tguyenn/Digital-Synthesizer/firmware/firmware_v1/Launchpad/Lab7_slidepot.png

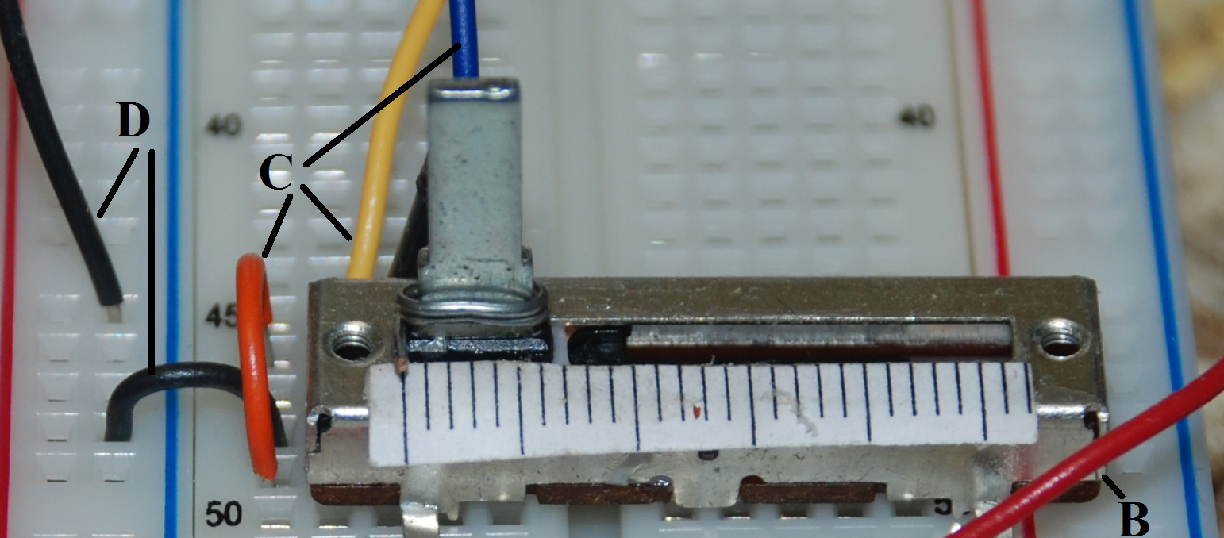
firmware/firmware_v1/Launchpad/Lab7_slidepot.png
