tguyenn/Digital-Synthesizer/firmware/inc/Motor.h

/*!
 * @defgroup RSLK
 * @brief RSLK motor interface
 <table>
<caption id="RSLKmotor pins">RSLK motor pins</caption>
<tr><th> TM4C <th> MSPM0  <th> Description
<tr><td> PF2  <td> PB4  <td> Motor_PWML, ML+, IN3, PB.4/TIMA1_C0;
<tr><td> PF3  <td> PB1  <td> Motor_PWMR, MR+, IN1, PB.1/TIMA1_C1;
<tr><td> PA3  <td> PB0  <td> Motor_DIR_L,ML-, IN4, 1 means forward, 0 means backward
<tr><td> PA2  <td> PB16 <td> Motor_DIR_R,MR-, IN2
</table>
 * @{*/
/**
 * @file      Motor.h
 * @brief     RSLK dual H-bridge driver
 * @details   RSLK motor interface<br>

 * @version   RSLK v2.02
 * @author    Daniel Valvano and Jonathan Valvano
 * @copyright Copyright 2024 by Jonathan W. Valvano, valvano@mail.utexas.edu,
 * @warning   AS-IS
 * @note      For more information see  http://users.ece.utexas.edu/~valvano/
 * @date      July 1, 2024
 <table>
<caption id="RSLKmotor2">RSLK motor pins</caption>
<tr><th> TM4C <th> MSPM0  <th> Description
<tr><td> PF2  <td> PB4  <td> Motor_PWML, ML+, IN3, PWM M1PWM6
<tr><td> PF3  <td> PB1  <td> Motor_PWMR, MR+, IN1, PWM M1PWM7
<tr><td> PA3  <td> PB0  <td> Motor_DIR_L,ML-, IN4, GPIO, 0 means forward, 1 means backward
<tr><td> PA2  <td> PB16 <td> Motor_DIR_R,MR-, IN2, GPIO, 0 means forward, 1 means backward
</table>
  ******************************************************************************/


#ifndef __MOTOR_H__
#define __MOTOR_H__
#include <stdint.h>
#define MOTOR_PERIOD 40000 // 12.5*4=50ns, 2ms
#define MOTORMIN 2
#define MOTORMAX (MOTOR_PERIOD-2)
/**
 * Initialize RSLK motors
 * PWM clock set to 50ns (divide by 4)
 * @param none
 * @return none
 * @brief  Initialize motors
 * @note period is 2000 us
 */
void Motor_Init(void);

/**
 * Set RSLK motor power forward<br>
 * @param dutyLeft MOTORMIN to MOTORMAX
 * @param dutyRight MOTORMIN to MOTORMAX
 * @return none
 * @note period is 10000 us
 * @brief  Go forward
 */
void Motor_Forward(uint32_t dutyLeft, uint32_t dutyRight);

/**
 * Set RSLK motor power backward<br>
 * @param dutyLeft MOTORMIN to MOTORMAX
 * @param dutyRight MOTORMIN to MOTORMAX
 * @return none
 * @note period is 2000 us
 * @brief  Go backward
 */
void Motor_Backward(uint32_t dutyLeft, uint32_t dutyRight);

/**
 * Set RSLK motor power right turn<br>
 * @param dutyLeft MOTORMIN to MOTORMAX
 * @param dutyRight MOTORMIN to MOTORMAX
 * @return none
 * @note period is 2000 us
 * @brief  Turn right
 */
void Motor_Right(uint32_t dutyLeft, uint32_t dutyRight);

/**
 * Set RSLK motor power left turn<br>
 * @param dutyLeft MOTORMIN to MOTORMAX
 * @param dutyRight MOTORMIN to MOTORMAX
 * @return none
 * @note period is 2000 us
 * @brief Turn left
 */
void Motor_Left(uint32_t dutyLeft, uint32_t dutyRight);

#endif
