tguyenn/Digital-Synthesizer/firmware/firmware_v1/inc/led_timer_regs.h

/*****************************************************************************

  Copyright (C) 2024 Texas Instruments Incorporated - http://www.ti.com/ 

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
   Neither the name of Texas Instruments Incorporated nor the names of
   its contributors may be used to endorse or promote products derived
   from this software without specific prior written permission.

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
*****************************************************************************/

#ifndef ti_devices_msp_peripherals_hw_gptimer__include
#define ti_devices_msp_peripherals_hw_gptimer__include

/* Filename: hw_gptimer.h */
/* Revised: 2024-06-04 10:48:04 */
/* Revision: a6be75578aae0bf7330b042a9fb5c36fc4988a43 */

#ifndef __CORTEX_M
  #ifdef __cplusplus
    #define __I  volatile        /*!< Defines 'read only' permissions */
  #else
    #define __I  volatile const  /*!< Defines 'read only' permissions */
  #endif
  #define __O  volatile          /*!< Defines 'write only' permissions */
  #define __IO  volatile         /*!< Defines 'read / write' permissions */

  /* following defines should be used for structure members */
  #define __IM  volatile const   /*! Defines 'read only' structure member permissions */
  #define __OM  volatile         /*! Defines 'write only' structure member permissions */
  #define __IOM  volatile        /*! Defines 'read / write' structure member permissions */
#endif

/* Use standard integer types with explicit width */
#include <stdint.h>

#ifdef __cplusplus
 extern "C" {
#endif

#if defined ( __CC_ARM )
#pragma anon_unions
#endif

/******************************************************************************
* GPTIMER Registers
******************************************************************************/
#define GPTIMER_COUNTERREGS_OFS                  ((uint32_t)0x00001800U)
#define GPTIMER_COMMONREGS_OFS                   ((uint32_t)0x00001100U)
#define GPTIMER_GEN_EVENT1_OFS                   ((uint32_t)0x00001080U)
#define GPTIMER_GEN_EVENT0_OFS                   ((uint32_t)0x00001050U)
#define GPTIMER_CPU_INT_OFS                      ((uint32_t)0x00001020U)
#define GPTIMER_GPRCM_OFS                        ((uint32_t)0x00000800U)


/** @addtogroup GPTIMER_COUNTERREGS
  @{
*/

typedef struct {
  __IO uint32_t CTR;                               /* !< (@ 0x00001800) Counter Register */
  __IO uint32_t CTRCTL;                            /* !< (@ 0x00001804) Counter Control Register */
  __IO uint32_t LOAD;                              /* !< (@ 0x00001808) Load Register */
       uint32_t RESERVED0;
  __IO uint32_t CC_01[2];                          /* !< (@ 0x00001810) Capture or Compare Register 0/1 */
  __IO uint32_t CC_23[2];                          /* !< (@ 0x00001818) Capture or Compare Register 2/3 */
  __IO uint32_t CC_45[2];                          /* !< (@ 0x00001820) The CC_45 register are a registers which can be
                                                      used as compare to the current CTR to create an events CC4U, CC4D,
                                                      CC5U and CC5D. */
       uint32_t RESERVED1[2];
  __IO uint32_t CCCTL_01[2];                       /* !< (@ 0x00001830) Capture or Compare Control Registers 0/1 */
  __IO uint32_t CCCTL_23[2];                       /* !< (@ 0x00001838) Capture or Compare Control Registers 2/3 */
  __IO uint32_t CCCTL_45[2];                       /* !< (@ 0x00001840) Capture or Compare Control Registers 4/5 */
       uint32_t RESERVED2[2];
  __IO uint32_t OCTL_01[2];                        /* !< (@ 0x00001850) CCP Output Control Registers 0/1 */
  __IO uint32_t OCTL_23[2];                        /* !< (@ 0x00001858) CCP Output Control Registers 2/3 */
       uint32_t RESERVED3[4];
  __IO uint32_t CCACT_01[2];                       /* !< (@ 0x00001870) Capture or Compare Action Registers 0/1 */
  __IO uint32_t CCACT_23[2];                       /* !< (@ 0x00001878) Capture or Compare Action Registers 2/3 */
  __IO uint32_t IFCTL_01[2];                       /* !< (@ 0x00001880) Input Filter Control Register 0/1 */
  __IO uint32_t IFCTL_23[2];                       /* !< (@ 0x00001888) Input Filter Control Register 2/3 */
       uint32_t RESERVED4[4];
  __IO uint32_t PL;                                /* !< (@ 0x000018A0) Phase Load Register */
  __IO uint32_t DBCTL;                             /* !< (@ 0x000018A4) Dead Band insertion control register */
       uint32_t RESERVED5[2];
  __IO uint32_t TSEL;                              /* !< (@ 0x000018B0) Trigger Select Register */
  __I  uint32_t RC;                                /* !< (@ 0x000018B4) Repeat counter Register */
  __IO uint32_t RCLD;                              /* !< (@ 0x000018B8) Repeat counter load Register */
  __I  uint32_t QDIR;                              /* !< (@ 0x000018BC) QEI Count Direction Register */
       uint32_t RESERVED6[4];
  __IO uint32_t FCTL;                              /* !< (@ 0x000018D0) Fault Control Register */
  __IO uint32_t FIFCTL;                            /* !< (@ 0x000018D4) Fault input Filter control register */
} GPTIMER_COUNTERREGS_Regs;

/*@}*/ /* end of group GPTIMER_COUNTERREGS */

/** @addtogroup GPTIMER_COMMONREGS
  @{
*/

typedef struct {
  __IO uint32_t CCPD;                              /* !< (@ 0x00001100) CCP Direction */
  __IO uint32_t ODIS;                              /* !< (@ 0x00001104) Output Disable */
  __IO uint32_t CCLKCTL;                           /* !< (@ 0x00001108) Counter Clock Control Register */
  __IO uint32_t CPS;                               /* !< (@ 0x0000110C) Clock Prescale Register */
  __I  uint32_t CPSV;                              /* !< (@ 0x00001110) Clock prescale count status register */
  __IO uint32_t CTTRIGCTL;                         /* !< (@ 0x00001114) Timer Cross Trigger Control Register */
       uint32_t RESERVED0;
  __O  uint32_t CTTRIG;                            /* !< (@ 0x0000111C) Timer Cross Trigger Register */
  __IO uint32_t FSCTL;                             /* !< (@ 0x00001120) Fault Source Control */
  __IO uint32_t GCTL;                              /* !< (@ 0x00001124) Global control register */
} GPTIMER_COMMONREGS_Regs;

/*@}*/ /* end of group GPTIMER_COMMONREGS */

/** @addtogroup GPTIMER_GEN_EVENT1
  @{
*/

typedef struct {
  __I  uint32_t IIDX;                              /* !< (@ 0x00001080) Interrupt index */
       uint32_t RESERVED0;
  __IO uint32_t IMASK;                             /* !< (@ 0x00001088) Interrupt mask */
       uint32_t RESERVED1;
  __I  uint32_t RIS;                               /* !< (@ 0x00001090) Raw interrupt status */
       uint32_t RESERVED2;
  __I  uint32_t MIS;                               /* !< (@ 0x00001098) Masked interrupt status */
       uint32_t RESERVED3;
  __O  uint32_t ISET;                              /* !< (@ 0x000010A0) Interrupt set */
       uint32_t RESERVED4;
  __O  uint32_t ICLR;                              /* !< (@ 0x000010A8) Interrupt clear */
} GPTIMER_GEN_EVENT1_Regs;

/*@}*/ /* end of group GPTIMER_GEN_EVENT1 */

/** @addtogroup GPTIMER_GEN_EVENT0
  @{
*/

typedef struct {
  __I  uint32_t IIDX;                              /* !< (@ 0x00001050) Interrupt index */
       uint32_t RESERVED0;
  __IO uint32_t IMASK;                             /* !< (@ 0x00001058) Interrupt mask */
       uint32_t RESERVED1;
  __I  uint32_t RIS;                               /* !< (@ 0x00001060) Raw interrupt status */
       uint32_t RESERVED2;
  __I  uint32_t MIS;                               /* !< (@ 0x00001068) Masked interrupt status */
       uint32_t RESERVED3;
  __O  uint32_t ISET;                              /* !< (@ 0x00001070) Interrupt set */
       uint32_t RESERVED4;
  __O  uint32_t ICLR;                              /* !< (@ 0x00001078) Interrupt clear */
} GPTIMER_GEN_EVENT0_Regs;

/*@}*/ /* end of group GPTIMER_GEN_EVENT0 */

/** @addtogroup GPTIMER_CPU_INT
  @{
*/

typedef struct {
  __I  uint32_t IIDX;                              /* !< (@ 0x00001020) Interrupt index */
       uint32_t RESERVED0;
  __IO uint32_t IMASK;                             /* !< (@ 0x00001028) Interrupt mask */
       uint32_t RESERVED1;
  __I  uint32_t RIS;                               /* !< (@ 0x00001030) Raw interrupt status */
       uint32_t RESERVED2;
  __I  uint32_t MIS;                               /* !< (@ 0x00001038) Masked interrupt status */
       uint32_t RESERVED3;
  __O  uint32_t ISET;                              /* !< (@ 0x00001040) Interrupt set */
       uint32_t RESERVED4;
  __O  uint32_t ICLR;                              /* !< (@ 0x00001048) Interrupt clear */
} GPTIMER_CPU_INT_Regs;

/*@}*/ /* end of group GPTIMER_CPU_INT */

/** @addtogroup GPTIMER_GPRCM
  @{
*/

typedef struct {
  __IO uint32_t PWREN;                             /* !< (@ 0x00000800) Power enable */
  __O  uint32_t RSTCTL;                            /* !< (@ 0x00000804) Reset Control */
       uint32_t RESERVED0[3];
  __I  uint32_t STAT;                              /* !< (@ 0x00000814) Status Register */
} GPTIMER_GPRCM_Regs;

/*@}*/ /* end of group GPTIMER_GPRCM */

/** @addtogroup GPTIMER
  @{
*/

typedef struct {
       uint32_t RESERVED0[256];
  __IO uint32_t FSUB_0;                            /* !< (@ 0x00000400) Subsciber Port 0 */
  __IO uint32_t FSUB_1;                            /* !< (@ 0x00000404) Subscriber Port 1 */
       uint32_t RESERVED1[15];
  __IO uint32_t FPUB_0;                            /* !< (@ 0x00000444) Publisher Port 0 */
  __IO uint32_t FPUB_1;                            /* !< (@ 0x00000448) Publisher Port 1 */
       uint32_t RESERVED2[237];
  GPTIMER_GPRCM_Regs  GPRCM;                             /* !< (@ 0x00000800) */
       uint32_t RESERVED3[506];
  __IO uint32_t CLKDIV;                            /* !< (@ 0x00001000) Clock Divider */
       uint32_t RESERVED4;
  __IO uint32_t CLKSEL;                            /* !< (@ 0x00001008) Clock Select for Ultra Low Power peripherals */
       uint32_t RESERVED5[3];
  __IO uint32_t PDBGCTL;                           /* !< (@ 0x00001018) Peripheral Debug Control */
       uint32_t RESERVED6;
  GPTIMER_CPU_INT_Regs  CPU_INT;                           /* !< (@ 0x00001020) */
       uint32_t RESERVED7;
  GPTIMER_GEN_EVENT0_Regs  GEN_EVENT0;                        /* !< (@ 0x00001050) */
       uint32_t RESERVED8;
  GPTIMER_GEN_EVENT1_Regs  GEN_EVENT1;                        /* !< (@ 0x00001080) */
       uint32_t RESERVED9[13];
  __IO uint32_t EVT_MODE;                          /* !< (@ 0x000010E0) Event Mode */
       uint32_t RESERVED10[6];
  __I  uint32_t DESC;                              /* !< (@ 0x000010FC) Module Description */
  GPTIMER_COMMONREGS_Regs  COMMONREGS;                        /* !< (@ 0x00001100) */
       uint32_t RESERVED11[438];
  GPTIMER_COUNTERREGS_Regs  COUNTERREGS;                       /* !< (@ 0x00001800) */
} GPTIMER_Regs;

/*@}*/ /* end of group GPTIMER */



#if defined ( __CC_ARM )
#pragma no_anon_unions
#endif

/******************************************************************************
* GPTIMER Register Control Bits
******************************************************************************/

/* GPTIMER_CTR Bits */
/* GPTIMER_CTR[CCTR] Bits */
#define GPTIMER_CTR_CCTR_OFS                     (0)                             /* !< CCTR Offset */
#define GPTIMER_CTR_CCTR_MASK                    ((uint32_t)0xFFFFFFFFU)         /* !< Current Counter value */
#define GPTIMER_CTR_CCTR_MINIMUM                 ((uint32_t)0x00000000U)         /* !< Minimum value */
#define GPTIMER_CTR_CCTR_MAXIMUM                 ((uint32_t)0xFFFFFFFFU)         /* !< Maximum Value */

/* GPTIMER_CTRCTL Bits */
/* GPTIMER_CTRCTL[EN] Bits */
#define GPTIMER_CTRCTL_EN_OFS                    (0)                             /* !< EN Offset */
#define GPTIMER_CTRCTL_EN_MASK                   ((uint32_t)0x00000001U)         /* !< Counter Enable.  This bit allows
                                                                                    the timer to advance  This bit is
                                                                                    automatically cleared if REPEAT=0 (do
                                                                                    not automatically reload) and the
                                                                                    counter value equals zero.  CPU
                                                                                    Write: A register write that sets the
                                                                                    EN bit, the counter value is set per
                                                                                    the CVAE value. Hardware: This bit
                                                                                    may also be set as the result of an
                                                                                    LCOND or ZCOND condition being met
                                                                                    and the counter value changed to the
                                                                                    load value or zero value,
                                                                                    respectively. */
#define GPTIMER_CTRCTL_EN_DISABLED               ((uint32_t)0x00000000U)         /* !< Disabled */
#define GPTIMER_CTRCTL_EN_ENABLED                ((uint32_t)0x00000001U)         /* !< Enabled */
/* GPTIMER_CTRCTL[REPEAT] Bits */
#define GPTIMER_CTRCTL_REPEAT_OFS                (1)                             /* !< REPEAT Offset */
#define GPTIMER_CTRCTL_REPEAT_MASK               ((uint32_t)0x0000000EU)         /* !< Repeat.  The repeat bit controls
                                                                                    whether the counter continues to
                                                                                    advance following a zero event, or
                                                                                    the exiting of a debug or fault
                                                                                    condition.  If counting down, a zero
                                                                                    event is followed by a load at the
                                                                                    next advance condition. If counting
                                                                                    up-down, a zero event is followed by
                                                                                    an advance event (+1). The intent of
                                                                                    encoding 3 is that if the debug
                                                                                    condition is in effect, the
                                                                                    generation of the load pulse is
                                                                                    deferred until the debug condition is
                                                                                    over. This allows the counter to
                                                                                    reach zero before counting is
                                                                                    suspended. */
#define GPTIMER_CTRCTL_REPEAT_REPEAT_0           ((uint32_t)0x00000000U)         /* !< Does not automatically advance
                                                                                    following a zero event. */
#define GPTIMER_CTRCTL_REPEAT_REPEAT_1           ((uint32_t)0x00000002U)         /* !< Continues to advance following a
                                                                                    zero event. */
#define GPTIMER_CTRCTL_REPEAT_REPEAT_2           ((uint32_t)0x00000004U)         /* !< Reserved */
#define GPTIMER_CTRCTL_REPEAT_REPEAT_3           ((uint32_t)0x00000006U)         /* !< Continues to advance following a
                                                                                    zero event if the debug mode is not
                                                                                    in effect, or following the release
                                                                                    of the debug mode. */
#define GPTIMER_CTRCTL_REPEAT_REPEAT_4           ((uint32_t)0x00000008U)         /* !< Reserved */
/* GPTIMER_CTRCTL[CM] Bits */
#define GPTIMER_CTRCTL_CM_OFS                    (4)                             /* !< CM Offset */
#define GPTIMER_CTRCTL_CM_MASK                   ((uint32_t)0x00000030U)         /* !< Count Mode */
#define GPTIMER_CTRCTL_CM_DOWN                   ((uint32_t)0x00000000U)         /* !< Down */
#define GPTIMER_CTRCTL_CM_UP_DOWN                ((uint32_t)0x00000010U)         /* !< Up/Down */
#define GPTIMER_CTRCTL_CM_UP                     ((uint32_t)0x00000020U)         /* !< Counter counts up. */
/* GPTIMER_CTRCTL[CVAE] Bits */
#define GPTIMER_CTRCTL_CVAE_OFS                  (28)                            /* !< CVAE Offset */
#define GPTIMER_CTRCTL_CVAE_MASK                 ((uint32_t)0x30000000U)         /* !< Counter Value After Enable.  This
                                                                                    field specifies the initialization
                                                                                    condition of the counter when the EN
                                                                                    bit is changed from 0 to 1 by a write
                                                                                    to the CTRCTL register. Note that an
                                                                                    external event can also cause the EN
                                                                                    bit to go active. */
#define GPTIMER_CTRCTL_CVAE_LDVAL                ((uint32_t)0x00000000U)         /* !< The counter is set to the LOAD
                                                                                    register value */
#define GPTIMER_CTRCTL_CVAE_NOCHANGE             ((uint32_t)0x10000000U)         /* !< The counter value is unchanged from
                                                                                    its current value which could have
                                                                                    been initialized by software */
#define GPTIMER_CTRCTL_CVAE_ZEROVAL              ((uint32_t)0x20000000U)         /* !< The counter is set to zero */
/* GPTIMER_CTRCTL[DRB] Bits */
#define GPTIMER_CTRCTL_DRB_OFS                   (17)                            /* !< DRB Offset */
#define GPTIMER_CTRCTL_DRB_MASK                  ((uint32_t)0x00020000U)         /* !< Debug Resume Behavior This bit
                                                                                    specifies what the device does
                                                                                    following the release/exit of debug
                                                                                    mode. */
#define GPTIMER_CTRCTL_DRB_RESUME                ((uint32_t)0x00000000U)         /* !< Resume counting */
#define GPTIMER_CTRCTL_DRB_CVAE_ACTION           ((uint32_t)0x00020000U)         /* !< Perform the action as specified by
                                                                                    the CVAE field. */
/* GPTIMER_CTRCTL[FB] Bits */
#define GPTIMER_CTRCTL_FB_OFS                    (18)                            /* !< FB Offset */
#define GPTIMER_CTRCTL_FB_MASK                   ((uint32_t)0x00040000U)         /* !< Fault Behavior This bit specifies
                                                                                    whether the counter continues running
                                                                                    or suspends during a fault mode.
                                                                                    There is a separate control under
                                                                                    REPEAT to indicate whether counting
                                                                                    is to suspend at next Counter==0 */
#define GPTIMER_CTRCTL_FB_CONT_COUNT             ((uint32_t)0x00000000U)         /* !< Continues counting */
#define GPTIMER_CTRCTL_FB_SUSP_COUNT             ((uint32_t)0x00040000U)         /* !< Suspends counting */
/* GPTIMER_CTRCTL[FRB] Bits */
#define GPTIMER_CTRCTL_FRB_OFS                   (19)                            /* !< FRB Offset */
#define GPTIMER_CTRCTL_FRB_MASK                  ((uint32_t)0x00080000U)         /* !< Fault Resume Behavior This bit
                                                                                    specifies what the device does
                                                                                    following the release/exit of fault
                                                                                    condition. */
#define GPTIMER_CTRCTL_FRB_RESUME                ((uint32_t)0x00000000U)         /* !< Resume counting */
#define GPTIMER_CTRCTL_FRB_CVAE_ACTION           ((uint32_t)0x00080000U)         /* !< Perform the action as specified by
                                                                                    the CVAE field. */
/* GPTIMER_CTRCTL[PLEN] Bits */
#define GPTIMER_CTRCTL_PLEN_OFS                  (24)                            /* !< PLEN Offset */
#define GPTIMER_CTRCTL_PLEN_MASK                 ((uint32_t)0x01000000U)         /* !< Phase Load Enable.  This bit allows
                                                                                    the timer to have phase load feature. */
#define GPTIMER_CTRCTL_PLEN_DISABLED             ((uint32_t)0x00000000U)         /* !< Disabled */
#define GPTIMER_CTRCTL_PLEN_ENABLED              ((uint32_t)0x01000000U)         /* !< Enabled */
/* GPTIMER_CTRCTL[SLZERCNEZ] Bits */
#define GPTIMER_CTRCTL_SLZERCNEZ_OFS             (23)                            /* !< SLZERCNEZ Offset */
#define GPTIMER_CTRCTL_SLZERCNEZ_MASK            ((uint32_t)0x00800000U)         /* !< Suppress Load and Zero Events if
                                                                                    Repeat Counter is Not Equal to Zero.
                                                                                    This bit suppresses the generation of
                                                                                    the Z (zero) and L (load) events from
                                                                                    the counter when the repeat counter
                                                                                    (RC) value is not 0. */
#define GPTIMER_CTRCTL_SLZERCNEZ_DISABLED        ((uint32_t)0x00000000U)         /* !< Disabled. Z and L events are always
                                                                                    generated from the counter when their
                                                                                    conditions are generated. */
#define GPTIMER_CTRCTL_SLZERCNEZ_ENABLED         ((uint32_t)0x00800000U)         /* !< Enabled. Z and L events are
                                                                                    generated from the counter when their
                                                                                    conditions are generated and the RC
                                                                                    register value is 0. */
/* GPTIMER_CTRCTL[CLC] Bits */
#define GPTIMER_CTRCTL_CLC_OFS                   (7)                             /* !< CLC Offset */
#define GPTIMER_CTRCTL_CLC_MASK                  ((uint32_t)0x00000380U)         /* !< Counter Load Control.  This field
                                                                                    specifies what controls the counter
                                                                                    operation with respect to setting the
                                                                                    counter to the LD register value.
                                                                                    Encodings 1-3 are present based on
                                                                                    the CCPC parameter value. Bits 4-5
                                                                                    are present based on the HQEI
                                                                                    parameter value. Any encodings not
                                                                                    provided are documented as reserved. */
#define GPTIMER_CTRCTL_CLC_CCCTL0_LCOND          ((uint32_t)0x00000000U)         /* !< CCCTL_0 LCOND */
#define GPTIMER_CTRCTL_CLC_CCCTL1_LCOND          ((uint32_t)0x00000080U)         /* !< CCCTL_1 LCOND */
#define GPTIMER_CTRCTL_CLC_CCCTL2_LCOND          ((uint32_t)0x00000100U)         /* !< CCCTL_2 LCOND This value exists
                                                                                    when there are 4 channels. */
#define GPTIMER_CTRCTL_CLC_CCCTL3_LCOND          ((uint32_t)0x00000180U)         /* !< CCCTL_3 LCOND This value exists
                                                                                    when there are 4 channels. */
#define GPTIMER_CTRCTL_CLC_QEI_2INP              ((uint32_t)0x00000200U)         /* !< Controlled by 2 input QEI mode.
                                                                                    This value exists when TIMER support
                                                                                    QEI feature. */
#define GPTIMER_CTRCTL_CLC_QEI_3INP              ((uint32_t)0x00000280U)         /* !< Controlled by 3 input QEI mode.
                                                                                    This value exists when TIMER support
                                                                                    QEI feature. */
/* GPTIMER_CTRCTL[CAC] Bits */
#define GPTIMER_CTRCTL_CAC_OFS                   (10)                            /* !< CAC Offset */
#define GPTIMER_CTRCTL_CAC_MASK                  ((uint32_t)0x00001C00U)         /* !< Counter Advance Control.  This
                                                                                    field specifies what controls the
                                                                                    counter operation with respect to
                                                                                    advancing (incrementing or
                                                                                    decrementing) the counter value.
                                                                                    Encodings 1-3 are present based on
                                                                                    the CCPC parameter value. Bits 4-5
                                                                                    are present based on the HQEI
                                                                                    parameter value. Any encodings not
                                                                                    provided are documented as reserved. */
#define GPTIMER_CTRCTL_CAC_CCCTL0_ACOND          ((uint32_t)0x00000000U)         /* !< CCCTL_0 ACOND */
#define GPTIMER_CTRCTL_CAC_CCCTL1_ACOND          ((uint32_t)0x00000400U)         /* !< CCCTL_1 ACOND */
#define GPTIMER_CTRCTL_CAC_CCCTL2_ACOND          ((uint32_t)0x00000800U)         /* !< CCCTL_2 ACOND This value exists
                                                                                    when there are 4 channels. */
#define GPTIMER_CTRCTL_CAC_CCCTL3_ACOND          ((uint32_t)0x00000C00U)         /* !< CCCTL_3 ACOND This value exists
                                                                                    when there are 4 channels. */
#define GPTIMER_CTRCTL_CAC_QEI_2INP              ((uint32_t)0x00001000U)         /* !< Controlled by 2-input QEI mode
                                                                                    This value exists when TIMER support
                                                                                    QEI feature. */
#define GPTIMER_CTRCTL_CAC_QEI_3INP              ((uint32_t)0x00001400U)         /* !< Controlled by 3-input QEI mode
                                                                                    This value exists when TIMER support
                                                                                    QEI feature. */
/* GPTIMER_CTRCTL[CZC] Bits */
#define GPTIMER_CTRCTL_CZC_OFS                   (13)                            /* !< CZC Offset */
#define GPTIMER_CTRCTL_CZC_MASK                  ((uint32_t)0x0000E000U)         /* !< Counter Zero Control This field
                                                                                    specifies what controls the counter
                                                                                    operation with respect to zeroing the
                                                                                    counter value.    Encodings 1-3 are
                                                                                    present based on the CCPC parameter
                                                                                    value. Bits 4-5 are present based on
                                                                                    the HQEI parameter value. Any
                                                                                    encodings not provided are documented
                                                                                    as reserved. */
#define GPTIMER_CTRCTL_CZC_CCCTL0_ZCOND          ((uint32_t)0x00000000U)         /* !< CCCTL_0 ZCOND */
#define GPTIMER_CTRCTL_CZC_CCCTL1_ZCOND          ((uint32_t)0x00002000U)         /* !< CCCTL_1 ZCOND */
#define GPTIMER_CTRCTL_CZC_CCCTL2_ZCOND          ((uint32_t)0x00004000U)         /* !< CCCTL_2 ZCOND This value exists
                                                                                    when there are 4 channels. */
#define GPTIMER_CTRCTL_CZC_CCCTL3_ZCOND          ((uint32_t)0x00006000U)         /* !< CCCTL_3 ZCOND This value exists
                                                                                    when there are 4 channels. */
#define GPTIMER_CTRCTL_CZC_QEI_2INP              ((uint32_t)0x00008000U)         /* !< Controlled by 2-input QEI mode
                                                                                    This value exists when TIMER support
                                                                                    QEI feature. */
#define GPTIMER_CTRCTL_CZC_QEI_3INP              ((uint32_t)0x0000A000U)         /* !< Controlled by 3-input QEI mode
                                                                                    This value exists when TIMER support
                                                                                    QEI feature. */

/* GPTIMER_LOAD Bits */
/* GPTIMER_LOAD[LD] Bits */
#define GPTIMER_LOAD_LD_OFS                      (0)                             /* !< LD Offset */
#define GPTIMER_LOAD_LD_MASK                     ((uint32_t)0xFFFFFFFFU)         /* !< Load Value */
#define GPTIMER_LOAD_LD_MINIMUM                  ((uint32_t)0x00000000U)         /* !< Minimum value */
#define GPTIMER_LOAD_LD_MAXIMUM                  ((uint32_t)0xFFFFFFFFU)         /* !< Maximum Value */

/* GPTIMER_CC_01 Bits */
/* GPTIMER_CC_01[CCVAL] Bits */
#define GPTIMER_CC_01_CCVAL_OFS                  (0)                             /* !< CCVAL Offset */
#define GPTIMER_CC_01_CCVAL_MASK                 ((uint32_t)0xFFFFFFFFU)         /* !< Capture or compare value */
#define GPTIMER_CC_01_CCVAL_MINIMUM              ((uint32_t)0x00000000U)         /* !< Minimum value */
#define GPTIMER_CC_01_CCVAL_MAXIMUM              ((uint32_t)0xFFFFFFFFU)         /* !< Maximum Value */

/* GPTIMER_CC_23 Bits */
/* GPTIMER_CC_23[CCVAL] Bits */
#define GPTIMER_CC_23_CCVAL_OFS                  (0)                             /* !< CCVAL Offset */
#define GPTIMER_CC_23_CCVAL_MASK                 ((uint32_t)0xFFFFFFFFU)         /* !< Capture or compare value */
#define GPTIMER_CC_23_CCVAL_MINIMUM              ((uint32_t)0x00000000U)         /* !< Minimum value */
#define GPTIMER_CC_23_CCVAL_MAXIMUM              ((uint32_t)0xFFFFFFFFU)         /* !< Maximum Value */

/* GPTIMER_CC_45 Bits */
/* GPTIMER_CC_45[CCVAL] Bits */
#define GPTIMER_CC_45_CCVAL_OFS                  (0)                             /* !< CCVAL Offset */
#define GPTIMER_CC_45_CCVAL_MASK                 ((uint32_t)0xFFFFFFFFU)         /* !< Capture or compare value */
#define GPTIMER_CC_45_CCVAL_MINIMUM              ((uint32_t)0x00000000U)         /* !< Minimum value */
#define GPTIMER_CC_45_CCVAL_MAXIMUM              ((uint32_t)0xFFFFFFFFU)         /* !< Maximum Value */
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
