tguyenn/Digital-Synthesizer/firmware/inc/hw_emac.h

//*****************************************************************************
//
// hw_emac.h - Macros used when accessing the EMAC hardware.
//
// Copyright (c) 2012-2014 Texas Instruments Incorporated.  All rights reserved.
// Software License Agreement
// 
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
//   Redistributions of source code must retain the above copyright
//   notice, this list of conditions and the following disclaimer.
// 
//   Redistributions in binary form must reproduce the above copyright
//   notice, this list of conditions and the following disclaimer in the
//   documentation and/or other materials provided with the  
//   distribution.
// 
//   Neither the name of Texas Instruments Incorporated nor the names of
//   its contributors may be used to endorse or promote products derived
//   from this software without specific prior written permission.
// 
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
// This is part of revision 2.1.0.12573 of the Tiva Firmware Development Package.
//
//*****************************************************************************

#ifndef __HW_EMAC_H__
#define __HW_EMAC_H__

//*****************************************************************************
//
// The following are defines for the EMAC register offsets.
//
//*****************************************************************************
#define EMAC_O_CFG              0x00000000  // Ethernet MAC Configuration
#define EMAC_O_FRAMEFLTR        0x00000004  // Ethernet MAC Frame Filter
#define EMAC_O_HASHTBLH         0x00000008  // Ethernet MAC Hash Table High
#define EMAC_O_HASHTBLL         0x0000000C  // Ethernet MAC Hash Table Low
#define EMAC_O_MIIADDR          0x00000010  // Ethernet MAC MII Address
#define EMAC_O_MIIDATA          0x00000014  // Ethernet MAC MII Data Register
#define EMAC_O_FLOWCTL          0x00000018  // Ethernet MAC Flow Control
#define EMAC_O_VLANTG           0x0000001C  // Ethernet MAC VLAN Tag
#define EMAC_O_STATUS           0x00000024  // Ethernet MAC Status
#define EMAC_O_RWUFF            0x00000028  // Ethernet MAC Remote Wake-Up
                                            // Frame Filter
#define EMAC_O_PMTCTLSTAT       0x0000002C  // Ethernet MAC PMT Control and
                                            // Status Register
#define EMAC_O_RIS              0x00000038  // Ethernet MAC Raw Interrupt
                                            // Status
#define EMAC_O_IM               0x0000003C  // Ethernet MAC Interrupt Mask
#define EMAC_O_ADDR0H           0x00000040  // Ethernet MAC Address 0 High
#define EMAC_O_ADDR0L           0x00000044  // Ethernet MAC Address 0 Low
                                            // Register
#define EMAC_O_ADDR1H           0x00000048  // Ethernet MAC Address 1 High
#define EMAC_O_ADDR1L           0x0000004C  // Ethernet MAC Address 1 Low
#define EMAC_O_ADDR2H           0x00000050  // Ethernet MAC Address 2 High
#define EMAC_O_ADDR2L           0x00000054  // Ethernet MAC Address 2 Low
#define EMAC_O_ADDR3H           0x00000058  // Ethernet MAC Address 3 High
#define EMAC_O_ADDR3L           0x0000005C  // Ethernet MAC Address 3 Low
#define EMAC_O_WDOGTO           0x000000DC  // Ethernet MAC Watchdog Timeout
#define EMAC_O_MMCCTRL          0x00000100  // Ethernet MAC MMC Control
#define EMAC_O_MMCRXRIS         0x00000104  // Ethernet MAC MMC Receive Raw
                                            // Interrupt Status
#define EMAC_O_MMCTXRIS         0x00000108  // Ethernet MAC MMC Transmit Raw
                                            // Interrupt Status
#define EMAC_O_MMCRXIM          0x0000010C  // Ethernet MAC MMC Receive
                                            // Interrupt Mask
#define EMAC_O_MMCTXIM          0x00000110  // Ethernet MAC MMC Transmit
                                            // Interrupt Mask
#define EMAC_O_TXCNTGB          0x00000118  // Ethernet MAC Transmit Frame
                                            // Count for Good and Bad Frames
#define EMAC_O_TXCNTSCOL        0x0000014C  // Ethernet MAC Transmit Frame
                                            // Count for Frames Transmitted
                                            // after Single Collision
#define EMAC_O_TXCNTMCOL        0x00000150  // Ethernet MAC Transmit Frame
                                            // Count for Frames Transmitted
                                            // after Multiple Collisions
#define EMAC_O_TXOCTCNTG        0x00000164  // Ethernet MAC Transmit Octet
                                            // Count Good
#define EMAC_O_RXCNTGB          0x00000180  // Ethernet MAC Receive Frame Count
                                            // for Good and Bad Frames
#define EMAC_O_RXCNTCRCERR      0x00000194  // Ethernet MAC Receive Frame Count
                                            // for CRC Error Frames
#define EMAC_O_RXCNTALGNERR     0x00000198  // Ethernet MAC Receive Frame Count
                                            // for Alignment Error Frames
#define EMAC_O_RXCNTGUNI        0x000001C4  // Ethernet MAC Receive Frame Count
                                            // for Good Unicast Frames
#define EMAC_O_VLNINCREP        0x00000584  // Ethernet MAC VLAN Tag Inclusion
                                            // or Replacement
#define EMAC_O_VLANHASH         0x00000588  // Ethernet MAC VLAN Hash Table
#define EMAC_O_TIMSTCTRL        0x00000700  // Ethernet MAC Timestamp Control
#define EMAC_O_SUBSECINC        0x00000704  // Ethernet MAC Sub-Second
                                            // Increment
#define EMAC_O_TIMSEC           0x00000708  // Ethernet MAC System Time -
                                            // Seconds
#define EMAC_O_TIMNANO          0x0000070C  // Ethernet MAC System Time -
                                            // Nanoseconds
#define EMAC_O_TIMSECU          0x00000710  // Ethernet MAC System Time -
                                            // Seconds Update
#define EMAC_O_TIMNANOU         0x00000714  // Ethernet MAC System Time -
                                            // Nanoseconds Update
#define EMAC_O_TIMADD           0x00000718  // Ethernet MAC Timestamp Addend
#define EMAC_O_TARGSEC          0x0000071C  // Ethernet MAC Target Time Seconds
#define EMAC_O_TARGNANO         0x00000720  // Ethernet MAC Target Time
                                            // Nanoseconds
#define EMAC_O_HWORDSEC         0x00000724  // Ethernet MAC System Time-Higher
                                            // Word Seconds
#define EMAC_O_TIMSTAT          0x00000728  // Ethernet MAC Timestamp Status
#define EMAC_O_PPSCTRL          0x0000072C  // Ethernet MAC PPS Control
#define EMAC_O_PPS0INTVL        0x00000760  // Ethernet MAC PPS0 Interval
#define EMAC_O_PPS0WIDTH        0x00000764  // Ethernet MAC PPS0 Width
#define EMAC_O_DMABUSMOD        0x00000C00  // Ethernet MAC DMA Bus Mode
#define EMAC_O_TXPOLLD          0x00000C04  // Ethernet MAC Transmit Poll
                                            // Demand
#define EMAC_O_RXPOLLD          0x00000C08  // Ethernet MAC Receive Poll Demand
#define EMAC_O_RXDLADDR         0x00000C0C  // Ethernet MAC Receive Descriptor
                                            // List Address
#define EMAC_O_TXDLADDR         0x00000C10  // Ethernet MAC Transmit Descriptor
                                            // List Address
#define EMAC_O_DMARIS           0x00000C14  // Ethernet MAC DMA Interrupt
                                            // Status
#define EMAC_O_DMAOPMODE        0x00000C18  // Ethernet MAC DMA Operation Mode
#define EMAC_O_DMAIM            0x00000C1C  // Ethernet MAC DMA Interrupt Mask
                                            // Register
#define EMAC_O_MFBOC            0x00000C20  // Ethernet MAC Missed Frame and
                                            // Buffer Overflow Counter
#define EMAC_O_RXINTWDT         0x00000C24  // Ethernet MAC Receive Interrupt
                                            // Watchdog Timer
#define EMAC_O_HOSTXDESC        0x00000C48  // Ethernet MAC Current Host
                                            // Transmit Descriptor
#define EMAC_O_HOSRXDESC        0x00000C4C  // Ethernet MAC Current Host
                                            // Receive Descriptor
#define EMAC_O_HOSTXBA          0x00000C50  // Ethernet MAC Current Host
                                            // Transmit Buffer Address
#define EMAC_O_HOSRXBA          0x00000C54  // Ethernet MAC Current Host
                                            // Receive Buffer Address
#define EMAC_O_PP               0x00000FC0  // Ethernet MAC Peripheral Property
                                            // Register
#define EMAC_O_PC               0x00000FC4  // Ethernet MAC Peripheral
                                            // Configuration Register
#define EMAC_O_CC               0x00000FC8  // Ethernet MAC Clock Configuration
                                            // Register
#define EMAC_O_EPHYRIS          0x00000FD0  // Ethernet PHY Raw Interrupt
                                            // Status
#define EMAC_O_EPHYIM           0x00000FD4  // Ethernet PHY Interrupt Mask
#define EMAC_O_EPHYMISC         0x00000FD8  // Ethernet PHY Masked Interrupt
                                            // Status and Clear
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
