tguyenn/Digital-Synthesizer/firmware/inc/hw_ints.h

//*****************************************************************************
//
// hw_ints.h - Macros that define the interrupt assignment on Stellaris.
//
// Copyright (c) 2005-2010 Texas Instruments Incorporated.  All rights reserved.
// Software License Agreement
// 
// Texas Instruments (TI) is supplying this software for use solely and
// exclusively on TI's microcontroller products. The software is owned by
// TI and/or its suppliers, and is protected under applicable copyright
// laws. You may not combine this software with "viral" open-source
// software in order to form a larger program.
// 
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
// This is part of revision 6075 of the Stellaris Firmware Development Package.
//
//*****************************************************************************

#ifndef __HW_INTS_H__
#define __HW_INTS_H__

//*****************************************************************************
//
// The following are defines for the fault assignments.
//
//*****************************************************************************
#define FAULT_NMI               2           // NMI fault
#define FAULT_HARD              3           // Hard fault
#define FAULT_MPU               4           // MPU fault
#define FAULT_BUS               5           // Bus fault
#define FAULT_USAGE             6           // Usage fault
#define FAULT_SVCALL            11          // SVCall
#define FAULT_DEBUG             12          // Debug monitor
#define FAULT_PENDSV            14          // PendSV
#define FAULT_SYSTICK           15          // System Tick
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
